ardagurbuuz/Lead-Compensator/ltspice/lead-compensator.asc

C1: cap; 10µ
C2: cap; 10µ
C3: cap; 10µ
C4: cap; 10µ
C5: cap; 1µ
C6: cap; 1µ
R1: res; 50k
R2: res; 100k
R3: res; 100k
R4: res; 10k
R5: res; 10k
R6: res; 10k
R7: res; 10k
R8: res; 50k
R9: res; 100k
R10: res; 100k
R11: res; 10k
R12: res; 10k
R13: res; 10k
R14: res; 10k
R15: res; 560k
R16: res; 165k
R17: res; 33k
R18: res; 102k
U1: UniversalOpAmp2
U2: UniversalOpAmp2
U3: UniversalOpAmp2
U4: UniversalOpAmp2
U5: UniversalOpAmp2
U6: UniversalOpAmp2
U7: UniversalOpAmp2
U8: UniversalOpAmp2
VCC: voltage; 12
VEE: voltage; 12
Vref: voltage; PULSE(0 1 0 1m 1m 100 200)
Named nets: 0
.tran 20
